kamikub/Pi-HAT/Simulations/LED/Buttons Sim/closed_GPIO_sim.png

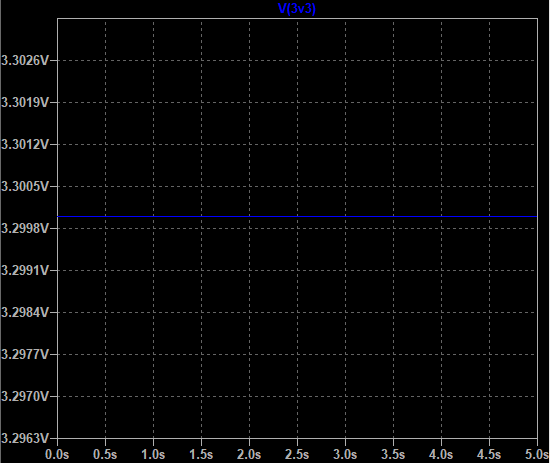
Simulations/LED/Buttons Sim/closed_GPIO_sim.png
