kamikub/Pi-HAT/Simulations/Power Supply Sim/PowerRegSim4V3.PNG

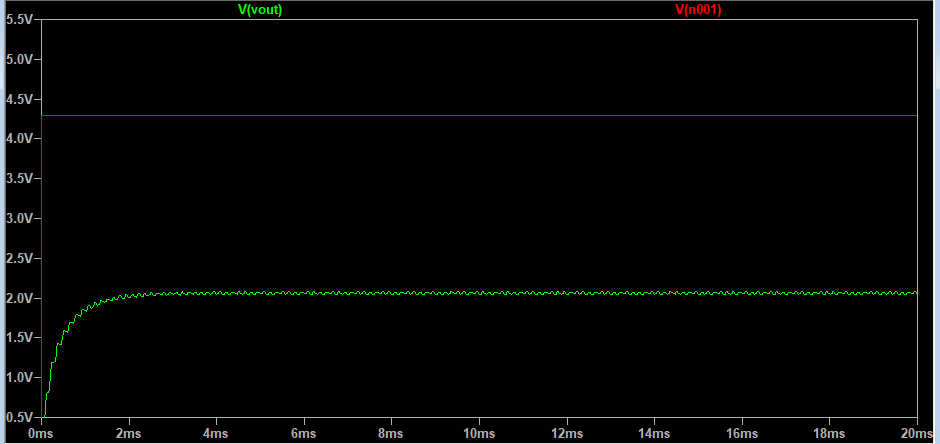
Simulations/Power Supply Sim/PowerRegSim4V3.PNG
