kamikub/Pi-HAT/Schematics/KiCad/Screenshots/OperationalAmplifier.PNG

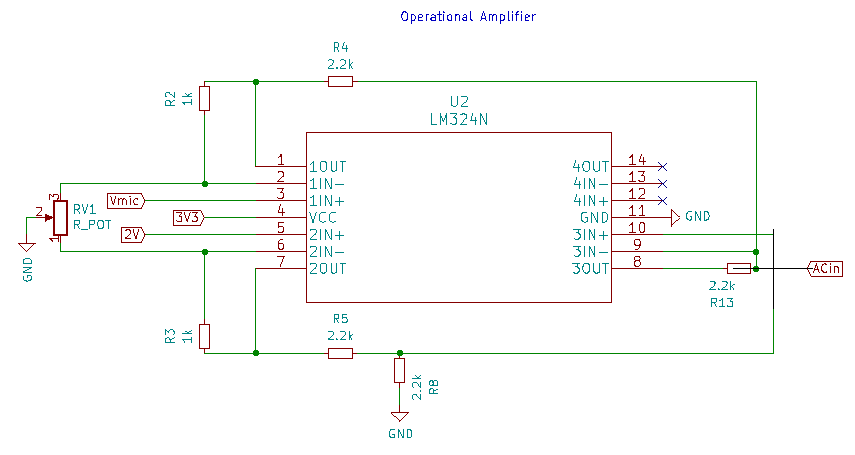
Schematics/KiCad/Screenshots/OperationalAmplifier.PNG
