kamikub/Pi-HAT/uHat integrated/meta/RPi_Zero_pHat_Template-F_Cu.pdf

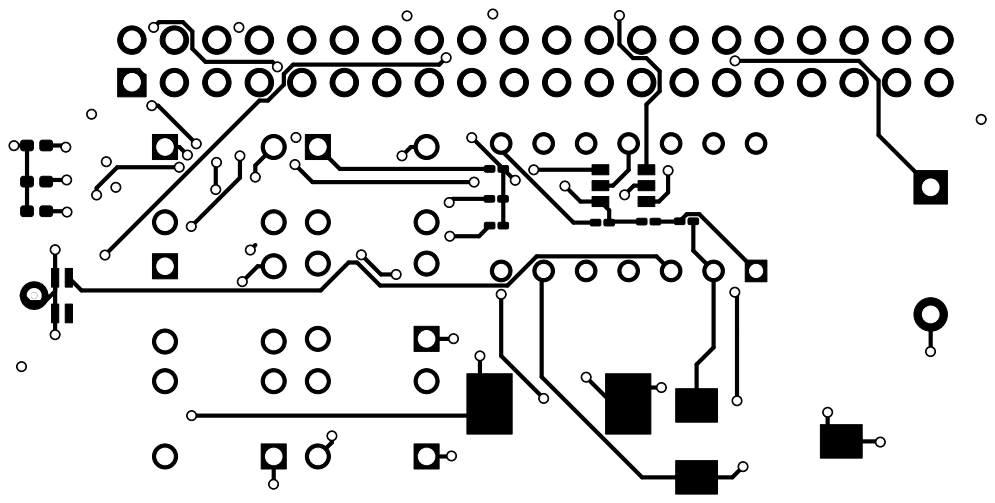
[picture p18: page 1]
