kamikub/Pi-HAT/uHat integrated/meta/RPi_Zero_pHat_Template-F_SilkS.pdf

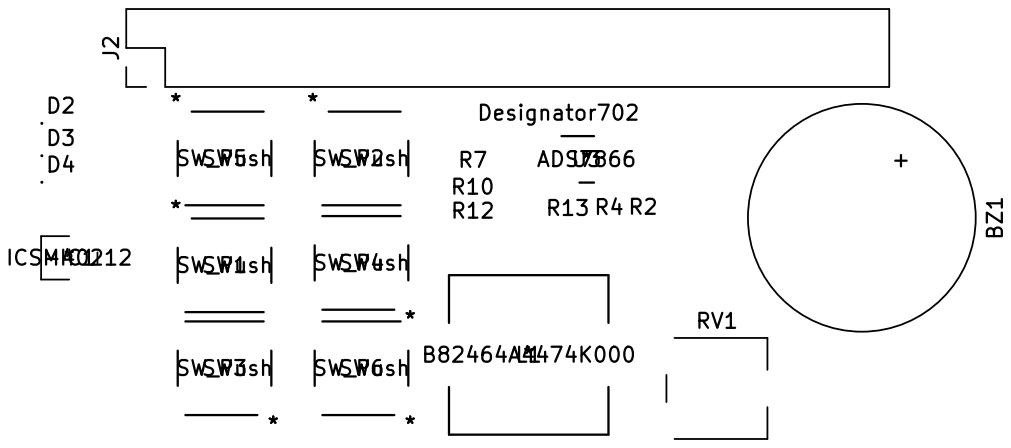
[picture p19: page 1]
