kamikub/Pi-HAT/uHat integrated/meta/RPi_Zero_pHat_Template-GND_Cu.pdf

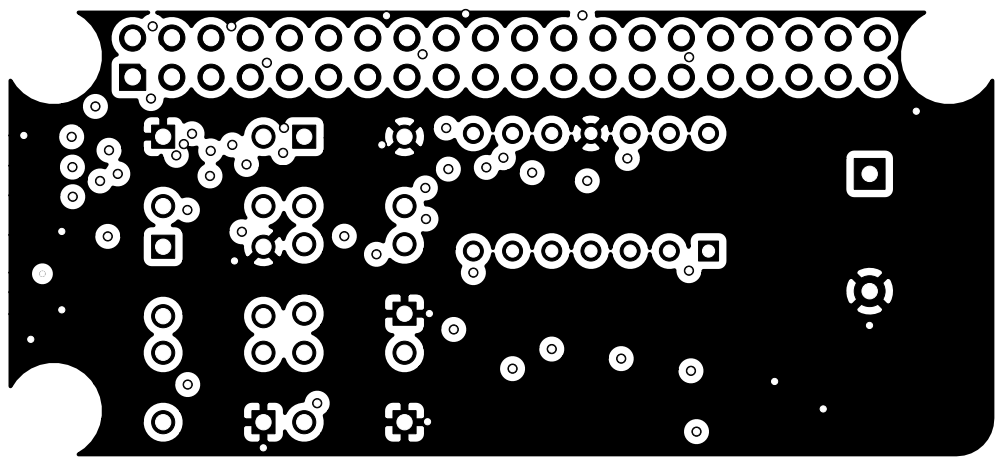
[picture p20: page 1]
