kamikub/Pi-HAT/Schematics/LTSpice/ADCHeaderLEDsbuttons.asc

40PinHeader: DIP40
D1: LED
D2: LED
D3: LED
R1: res
R2: res
R3: res
R4: res
R5: res
R6: res
R7: res
R8: res
R9: res
U1: AD7866
X1: buzzer
Named nets: 0, 3v3, GPIO, CS, SCLK, MISO, CE0, Opamp_out, 5V, PWM
Each GPIO pin from 40PinHeader corrisponds with a single GPIO from the other parrts of the cct
