kamikub/Pi-HAT/Schematics/LTSpice/Amplifier.asc

R1: res; 1k
R2: res; 1k
R3: res; 2.2k
R4: res; 2.2k
R5: res; 2.2k
R6: res; 2.2k
R7: res; 33k
U1: OP07
U2: OP07
U3: OP07
V1: voltage; SINE(0 0.63 10)
V2: voltage; SINE(0 2 10)
V4: voltage; 3.3
V5: voltage; 3.3
V7: voltage; 3.3
Named nets: 0, Opamp_out
.tran 0 1 0 0.001
