kamikub/Pi-HAT/Schematics/LTSpice/Power_Reg_Circuit.asc

C1: cap; 22µ; V=226M006ATE028 Rser=0 Lser=0 mfg="Murata" pn="GRM188R60G226MEA0" type="X5R"
D1: diode; 1N914
L1: ind; 470µ; Ipk=620m Rser=1.15 Rpar=347.989K Cpar=0 mfg="Bourns, Inc." pn="SRR0908-471YL"
M1: nmos; FDW2503NZ
Pi_5V: voltage; 5
Pi_PWM: voltage; PULSE(0 3.3 0 0 0 57.143u 142.86u)
R1: res; 100
RL: res; 200
Named nets: Vout, 0
.tran 20m uic
