kamikub/Pi-HAT/Schematics/KiCad/Integrated_Schematic.sch

## KiCad design Schematics/KiCad/Integrated_Schematic.sch (2021-06-04)

Schematic: Integrated_Schematic.sch

Parts:
BZ1: 535-8253; Buzzer_15x7.5RM7.6
C1: LMK107BBJ226MA-T
D1: LED-Y; LED_0402_1005Metric_Pad0.77x0.64mm_HandSolder
D2: LED-G; LED_0402_1005Metric_Pad0.77x0.64mm_HandSolder
D3: LED-R; LED_0402_1005Metric_Pad0.77x0.64mm_HandSolder
D4: 1N914; D_DO-35_SOD27_P7.62mm_Horizontal
J1: Connector-ML_RPi_GPIO; Samtec_HLE-120-02-xxx-DV-BE-A_2x20_RPi_Top
L1: B82464A4474K000
R1, R2: 1k; R_Axial_DIN0204_L3.6mm_D1.6mm_P1.90mm_Vertical
R3, R4, R7, R8, R10, R11: 10k; R_Axial_DIN0204_L3.6mm_D1.6mm_P1.90mm_Vertical
R5, R6, R9, R12: 2.2k; R_Axial_DIN0204_L3.6mm_D1.6mm_P1.90mm_Vertical
R13, R14, R15, R16: 100; R_Axial_DIN0204_L3.6mm_D1.6mm_P1.90mm_Vertical
R17: 200; R_Axial_DIN0204_L3.6mm_D1.6mm_P1.90mm_Vertical
RV1: R_POT; Potentiometer_ACP_CA9-V10_Vertical
SW1, SW2, SW3, SW4, SW5, SW6: SW_Push; 1825910-6
U1: LM324N
U2: ADS7866; ADS7866IDBVT
U3: FDW2503NZ
U4: ADMP504ACEZ-RL

Notes on the sheet:
40 pin header
Quad op amp
Frequency Tuner Integrated Schematic: uHat
2021/06/04
Power Supply
This is the schematic of Group 18's uHat design of a frequency tuner. Power supply and op amps are connected to the 40 pin header by means of labelling nodes.
Authors: BTJLUK001, KMLSAL001, ZLLJUL001
