kamikub/Pi-HAT/Schematics/KiCad/LED_Buttons_ADC.sch

## KiCad design Schematics/KiCad/LED_Buttons_ADC.sch (2021-06-04)

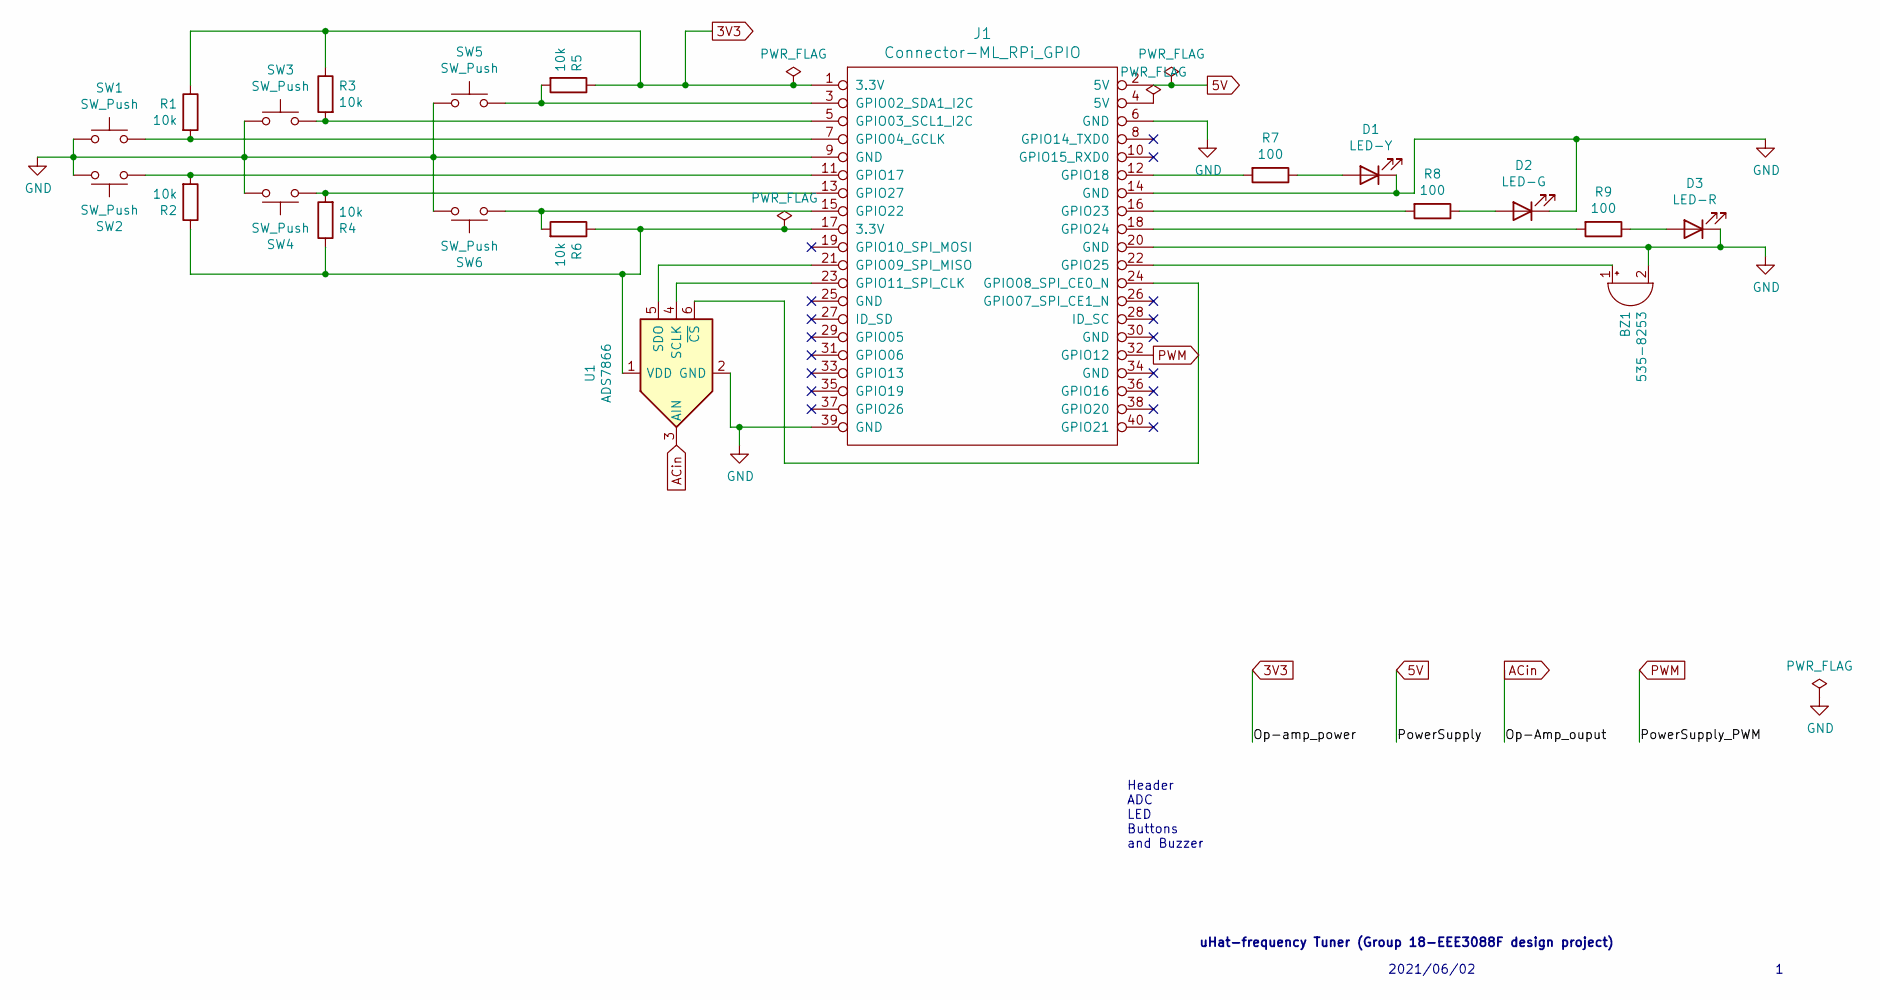
[picture p24: schematic LED_Buttons_ADC.sch]

Parts:
BZ1: 535-8253
D1: LED-Y
D2: LED-G
D3: LED-R
J1: Connector-ML_RPi_GPIO; Samtec_HLE-120-02-xxx-DV-BE-A_2x20_RPi_Top
R1, R2, R3, R4, R5, R6: 10k
R7, R8, R9: 100
SW1, SW2, SW3, SW4, SW5, SW6: SW_Push
U1: ADS7866

Connections:
3V3: J1.1 (3.3V), R1.1, R3.1, R5.1
5V: J1.2 (5V)
ACin: U1.3 (AIN)
GND: BZ1.2 (+), D1.1 (K), D2.1 (K), D3.1 (K), J1.6 (GND), J1.9 (GND), J1.14 (GND), J1.20 (GND), J1.39 (GND), SW1.2, SW2.2, SW3.1, SW4.1, SW5.1, SW6.1, U1.2 (GND)
unnamed: BZ1.1 (-), J1.22 (GPIO25)
unnamed: D1.2 (A), R7.1
unnamed: D2.2 (A), R8.1
unnamed: D3.2 (A), R9.1
unnamed: J1.3 (GPIO02_SDA1_I2C), R5.2, SW5.2
unnamed: J1.5 (GPIO03_SCL1_I2C), R3.2, SW3.2
unnamed: J1.7 (GPIO04_GCLK), R1.2, SW1.1
unnamed: J1.11 (GPIO17), R2.2, SW2.1
unnamed: J1.12 (GPIO18), R7.2
unnamed: J1.13 (GPIO27), R4.2, SW4.2
unnamed: J1.15 (GPIO22), R6.2, SW6.2
unnamed: J1.16 (GPIO23), R8.2
unnamed: J1.17 (3.3V), R2.1, R4.1, R6.1, U1.1 (VDD)
unnamed: J1.18 (GPIO24), R9.2
unnamed: J1.21 (GPIO09_SPI_MISO), U1.5 (SDO)
unnamed: J1.23 (GPIO11_SPI_CLK), U1.4 (SCLK)
unnamed: J1.24 (GPIO08_SPI_CE0_N), U1.6 (~CS)
PWM: J1.32 (GPIO12)

Notes on the sheet:
2021/06/02
Header ADC LED Buttons and Buzzer
uHat-frequency Tuner (Group 18-EEE3088F design project)
