kamikub/Pi-HAT/Schematics/KiCad/PowerSupply.sch

## KiCad design Schematics/KiCad/PowerSupply.sch (2021-06-09)

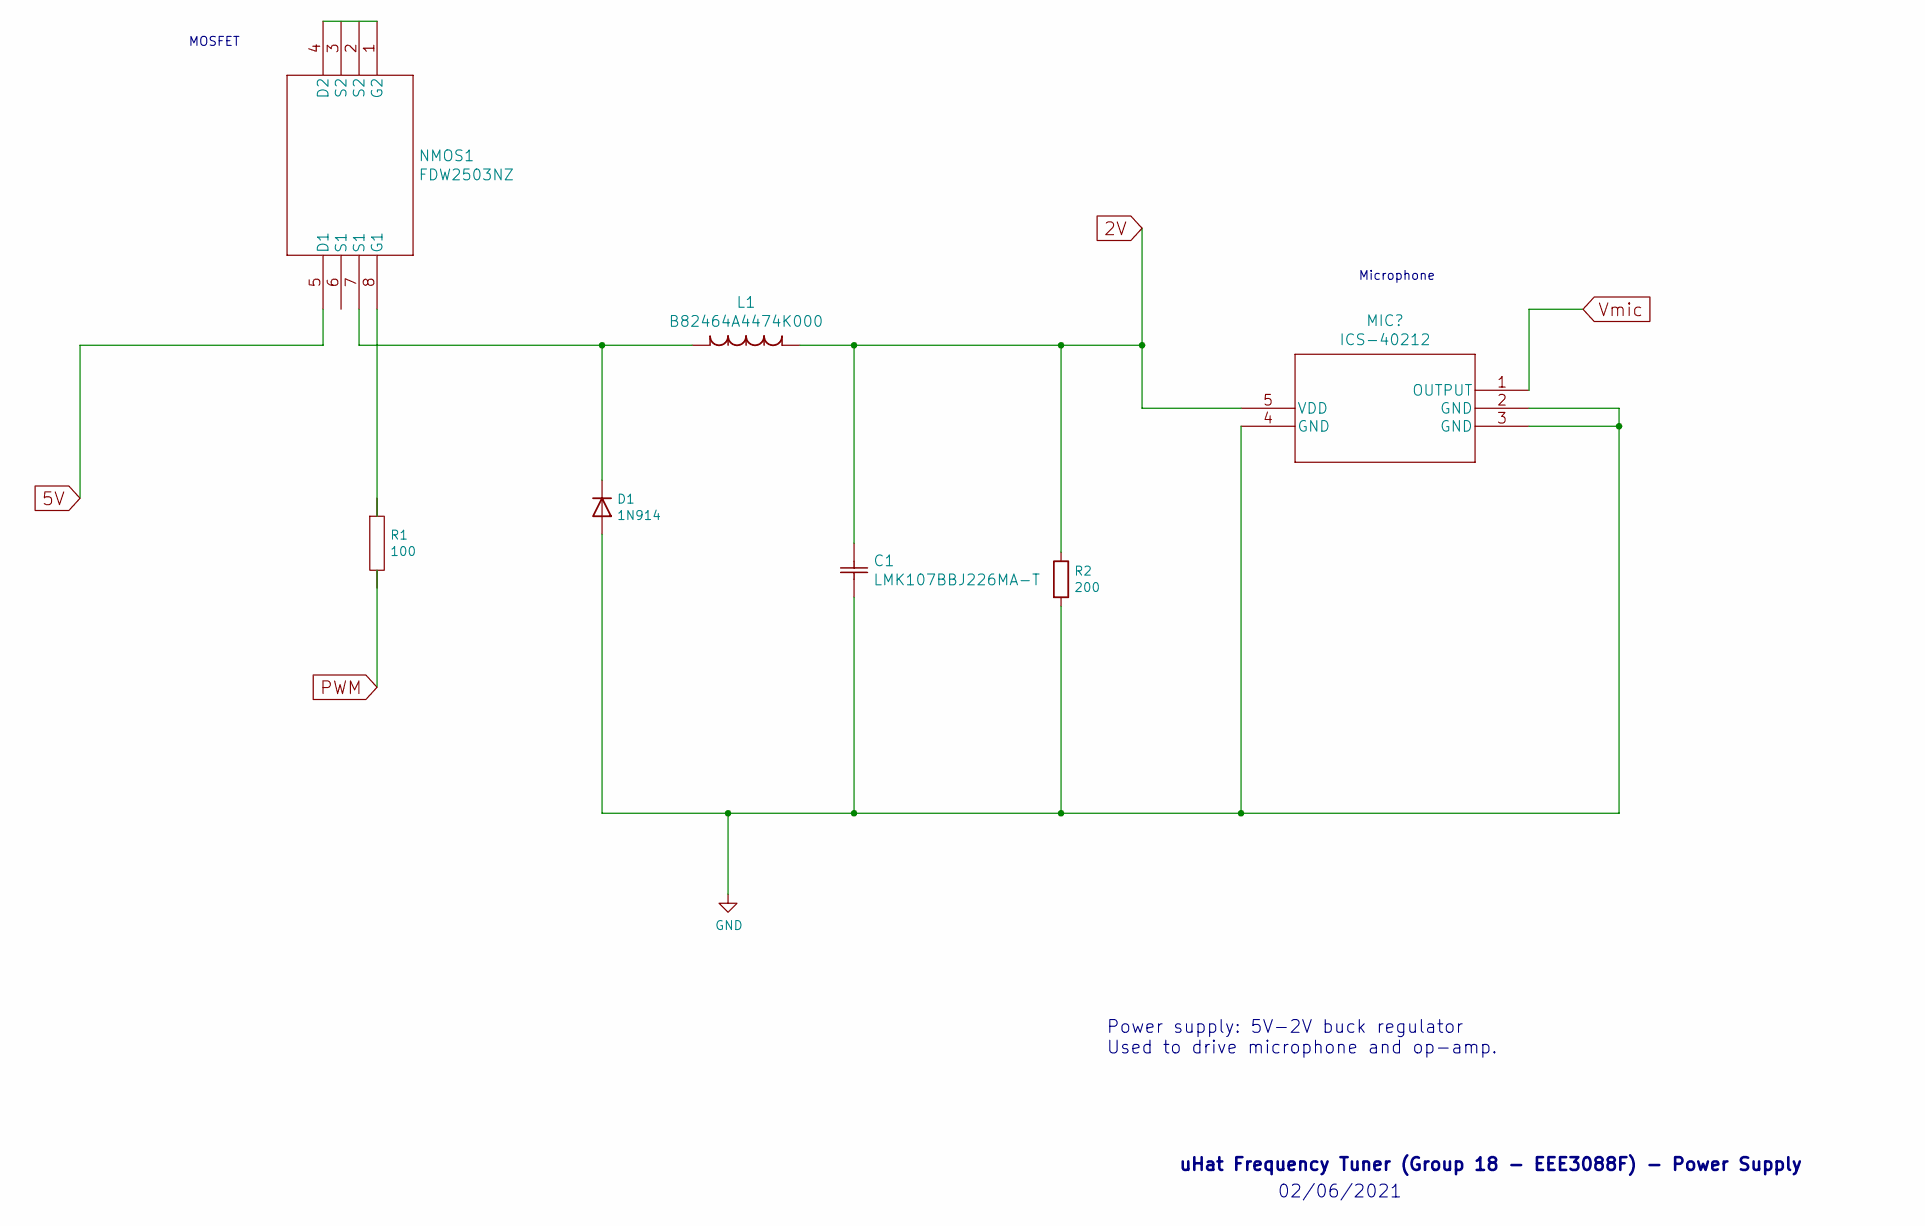
[picture p25: schematic PowerSupply.sch]

Parts:
C1: LMK107BBJ226MA-T
D1: 1N914; D_0402_1005Metric
L1: B82464A4474K000
NMOS1: FDW2503NZ
R1: 100; R_Axial_DIN0204_L3.6mm_D1.6mm_P5.08mm_Vertical
R2: 200; R_Axial_DIN0204_L3.6mm_D1.6mm_P5.08mm_Vertical

Connections:
2V: C1.1, L1.1, R2.1
5V: NMOS1.5 (D1)
GND: C1.2, D1.2 (A), R2.2
unnamed: D1.1 (K), L1.2, NMOS1.7 (S1)
unnamed: NMOS1.1 (G2), NMOS1.4 (D2)

Notes on the sheet:
uHat Frequency Tuner (Group 18 - EEE3088F) - Power Supply
02/06/2021
Power supply: 5V-2V buck regulator Used to drive microphone and op-amp.
MOSFET
Microphone
